jmpinit/mechane/soft/demo/Processing/mine/demo/data/png.png

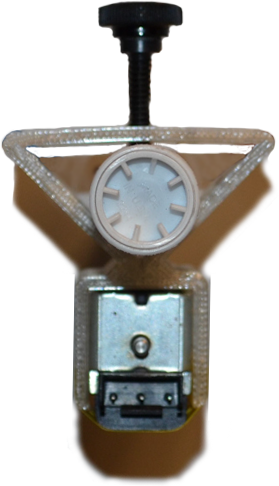
soft/demo/Processing/mine/demo/data/png.png
