jmpinit/mechane/hard/eyecandy/final/final-exploded.png

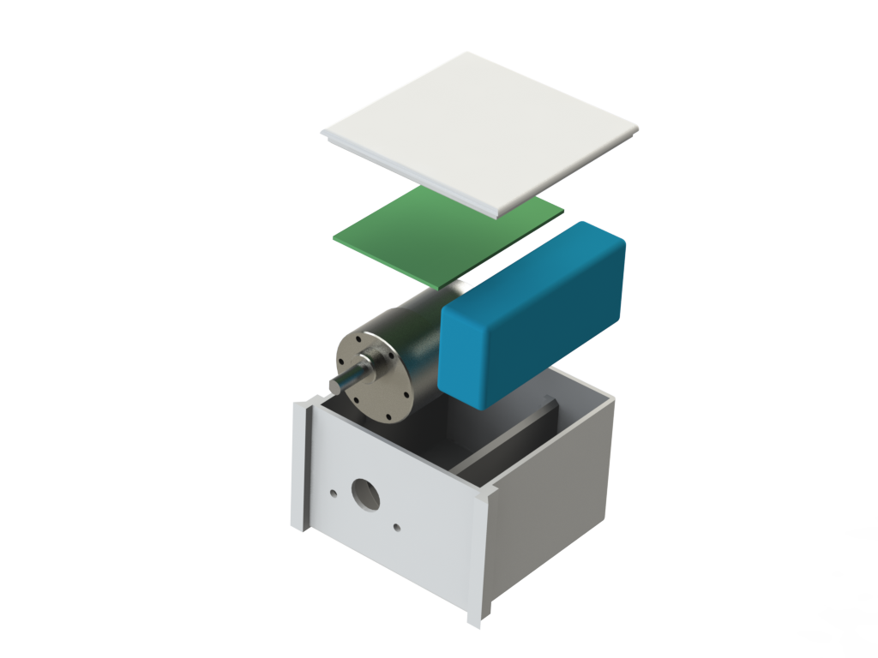
hard/eyecandy/final/final-exploded.png
