jmpinit/mechane/hard/CAD/back.SLDPRT

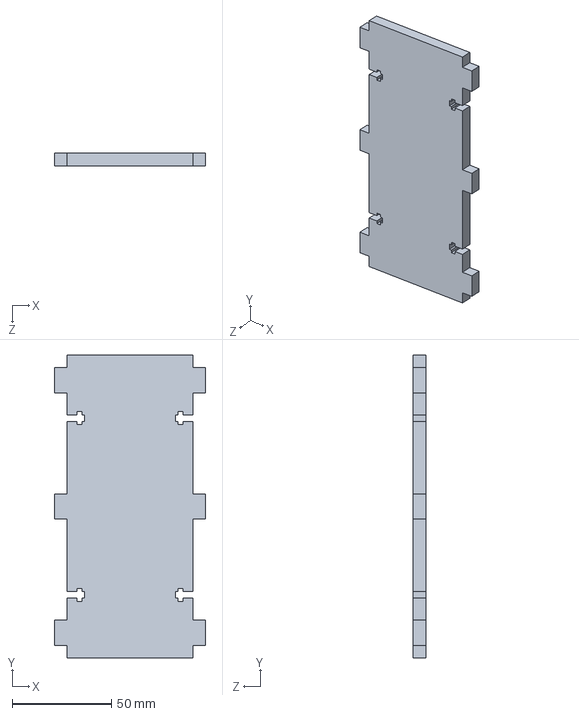
[picture p24: CAD file, 2013-10-06]
hard/CAD/back.SLDPRT
76.2 x 152.4 x 6.35 mm
