jmpinit/mechane/hard/CAD/clamp2.SLDPRT

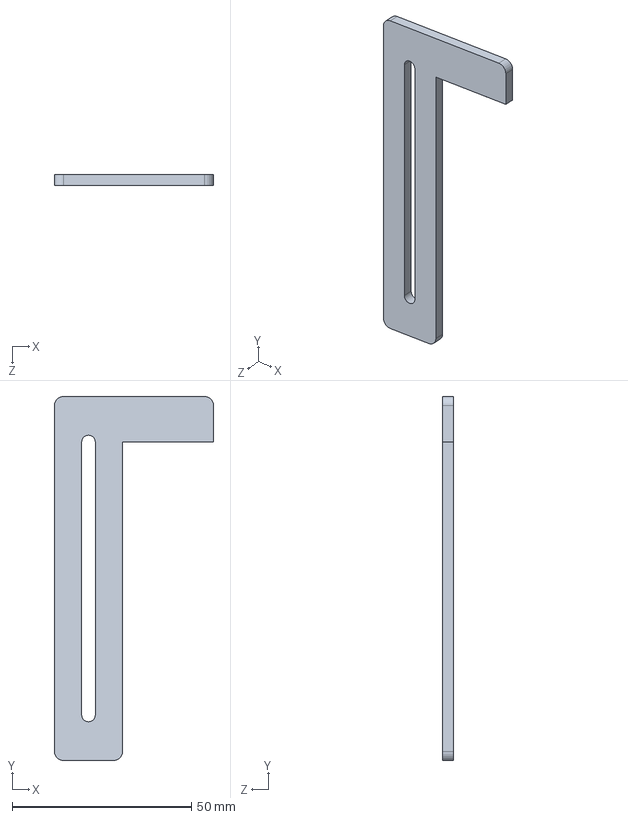
[picture p25: CAD file, 2013-10-06]
hard/CAD/clamp2.SLDPRT
44.5 x 101.6 x 3.17 mm
