jmpinit/mechane/hard/CAD/stepper_faceplate.SLDPRT

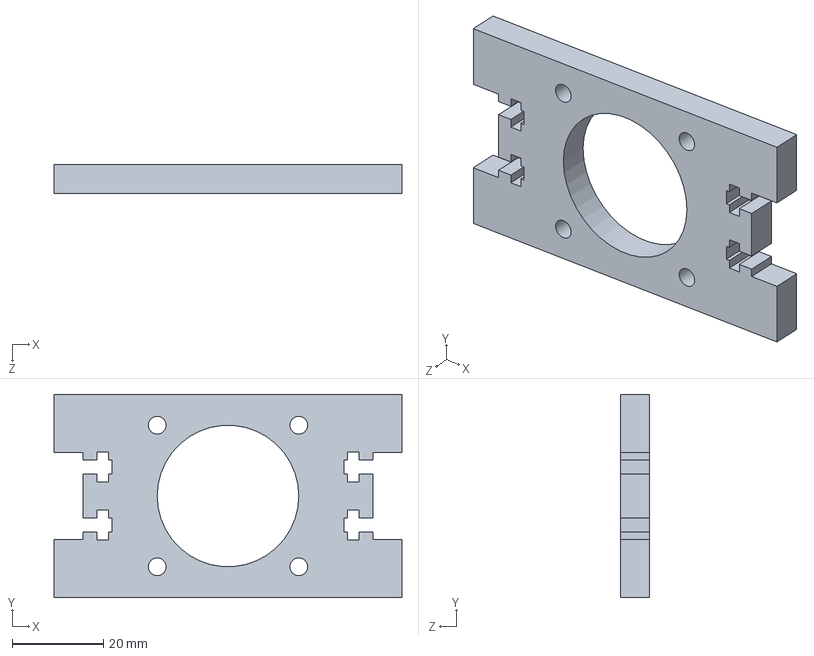
[picture p26: CAD file, 2013-10-06]
hard/CAD/stepper_faceplate.SLDPRT
76.2 x 44.5 x 6.35 mm
