jmpinit/mechane/hard/CADv2/gear_motor.SLDPRT

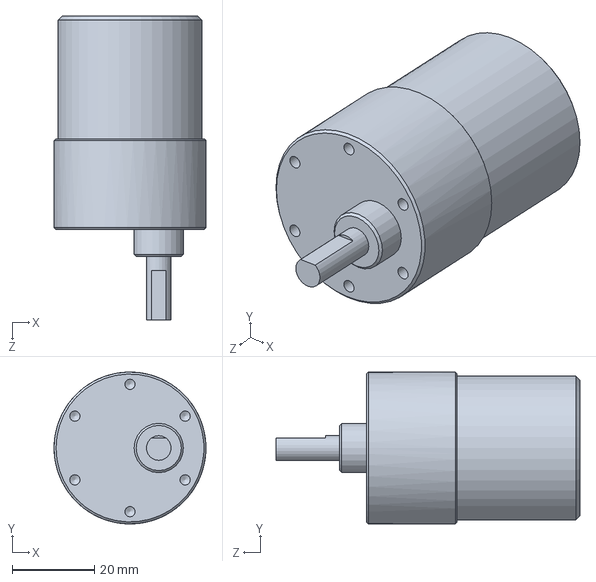
[picture p27: CAD file, 2014-02-02]
hard/CADv2/gear_motor.SLDPRT
37.0 x 37.0 x 74.0 mm
