jmpinit/mechane/hard/CAD/clamp1.SLDPRT

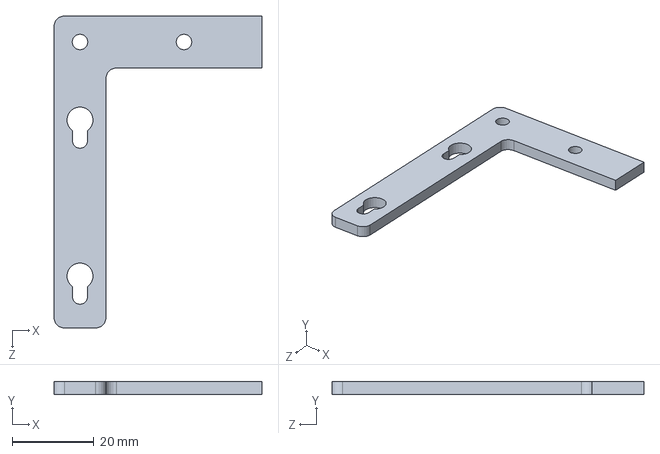
[picture p28: CAD file, 2013-10-06]
hard/CAD/clamp1.SLDPRT
50.8 x 3.17 x 76.2 mm
