jmpinit/mechane/hard/CADv2/bottomcase.sldprt

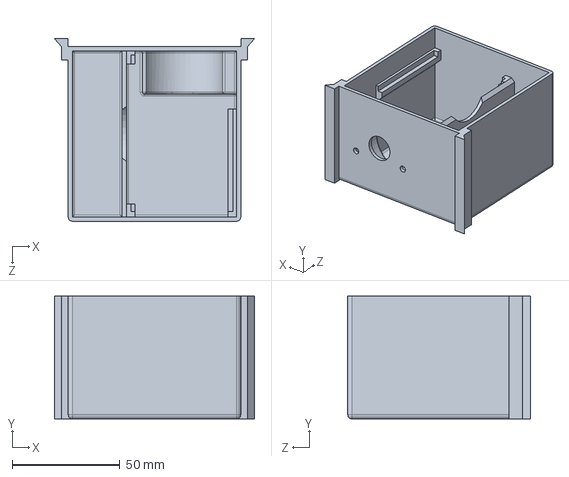
[picture p29: CAD file, 2014-02-02]
hard/CADv2/bottomcase.sldprt
92.7 x 57.0 x 84.6 mm
