jmpinit/mechane/hard/CAD/kinematic_coupler.SLDPRT

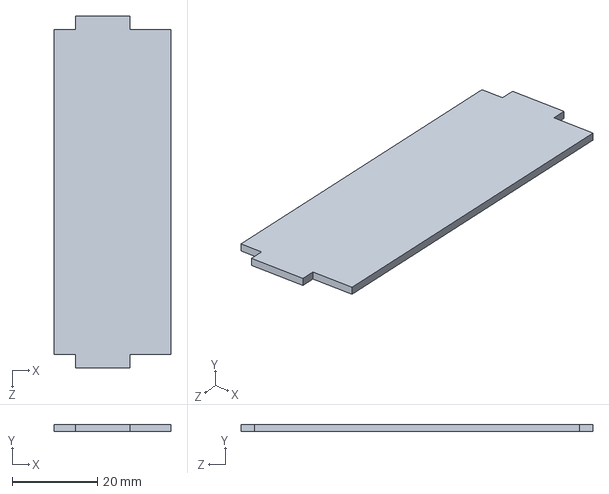
[picture p30: CAD file, 2013-10-05]
hard/CAD/kinematic_coupler.SLDPRT
27.4 x 1.59 x 82.5 mm
