jmpinit/mechane/hard/CAD/carriage.SLDPRT

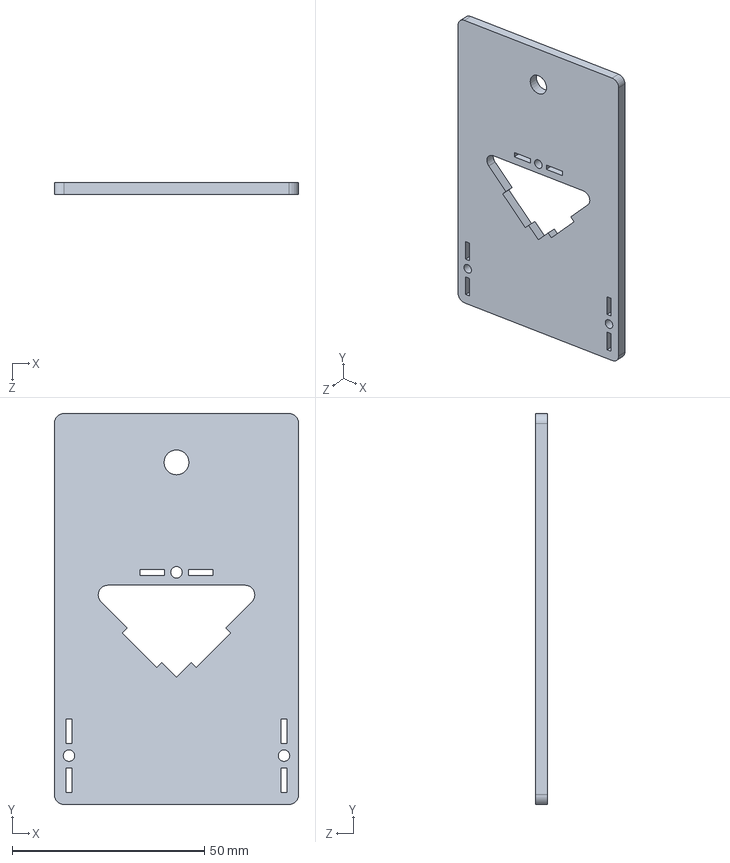
[picture p31: CAD file, 2013-10-05]
hard/CAD/carriage.SLDPRT
63.5 x 101.6 x 3.17 mm
