jmpinit/mechane/hard/CAD/nema17.SLDPRT

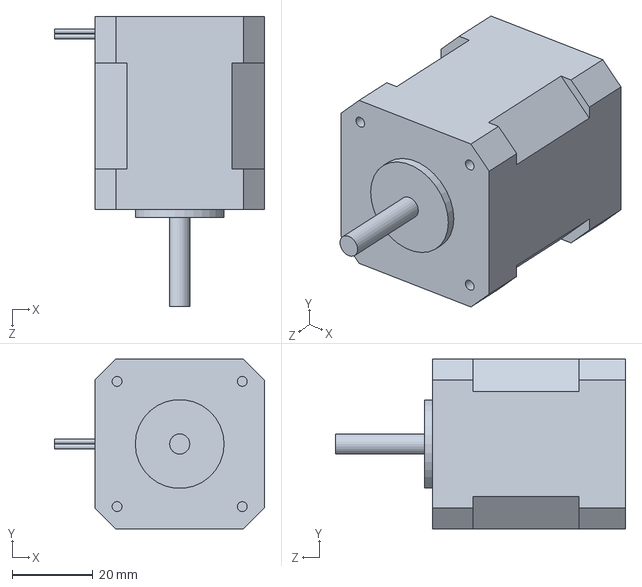
[picture p32: CAD file, 2013-10-05]
hard/CAD/nema17.SLDPRT
52.0 x 42.0 x 71.8 mm
