jmpinit/mechane/hard/CAD/pcb_volumedummy.SLDPRT

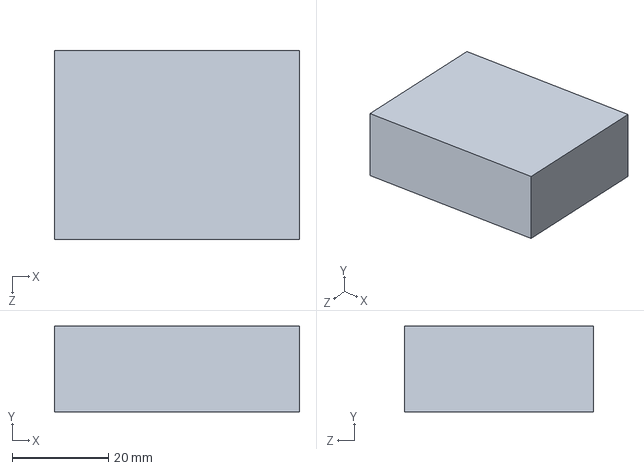
[picture p33: CAD file, 2013-10-05]
hard/CAD/pcb_volumedummy.SLDPRT
50.8 x 17.8 x 39.1 mm
