jmpinit/mechane/hard/CAD/printhead.SLDPRT

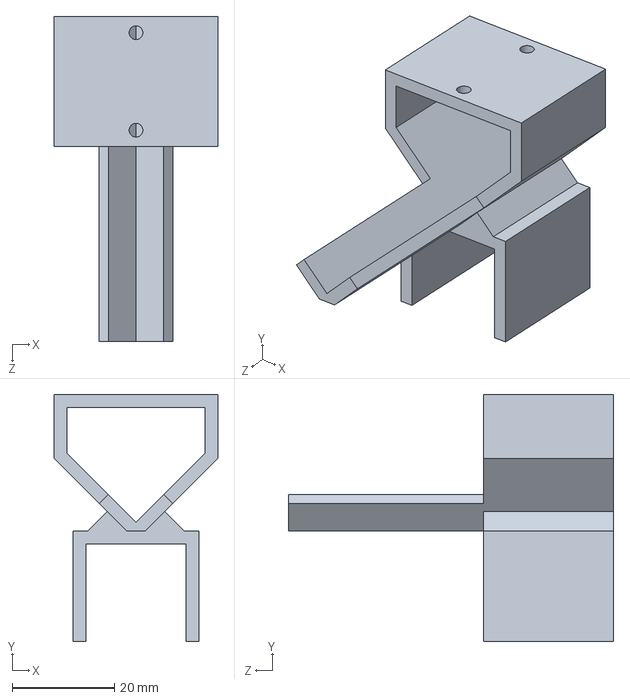
[picture p34: CAD file, 2013-10-05]
hard/CAD/printhead.SLDPRT
32.0 x 48.2 x 63.5 mm
