jmpinit/mechane/hard/CADv2/test_orientation.png

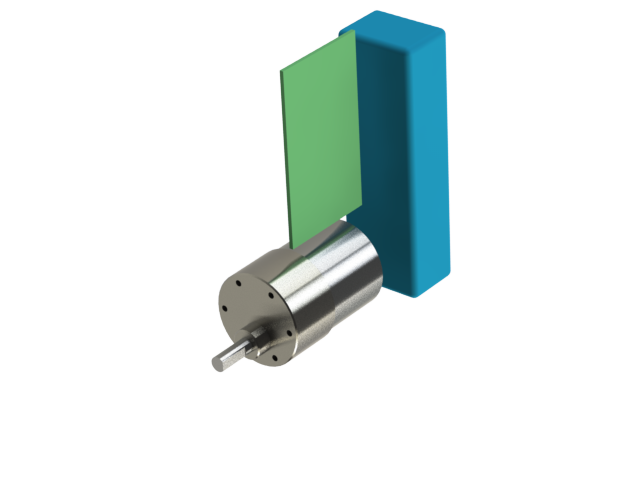
hard/CADv2/test_orientation.png
